omdathetkan/testrack/Boards/Backplane/Documentation/rework-reva-address-pullup.png

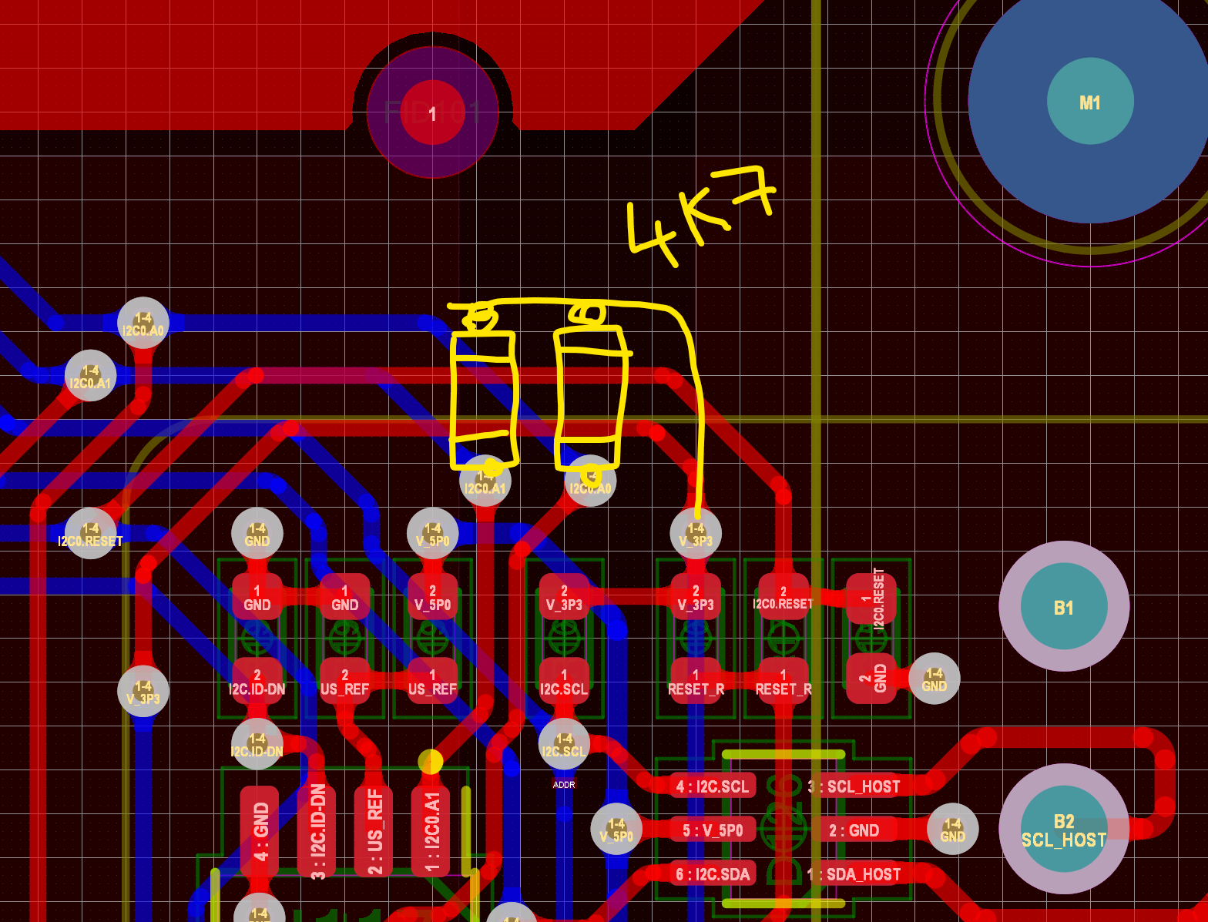
Boards/Backplane/Documentation/rework-reva-address-pullup.png
