omdathetkan/testrack/Boards/Backplane/Documentation/rework-reva-i2cmux.png

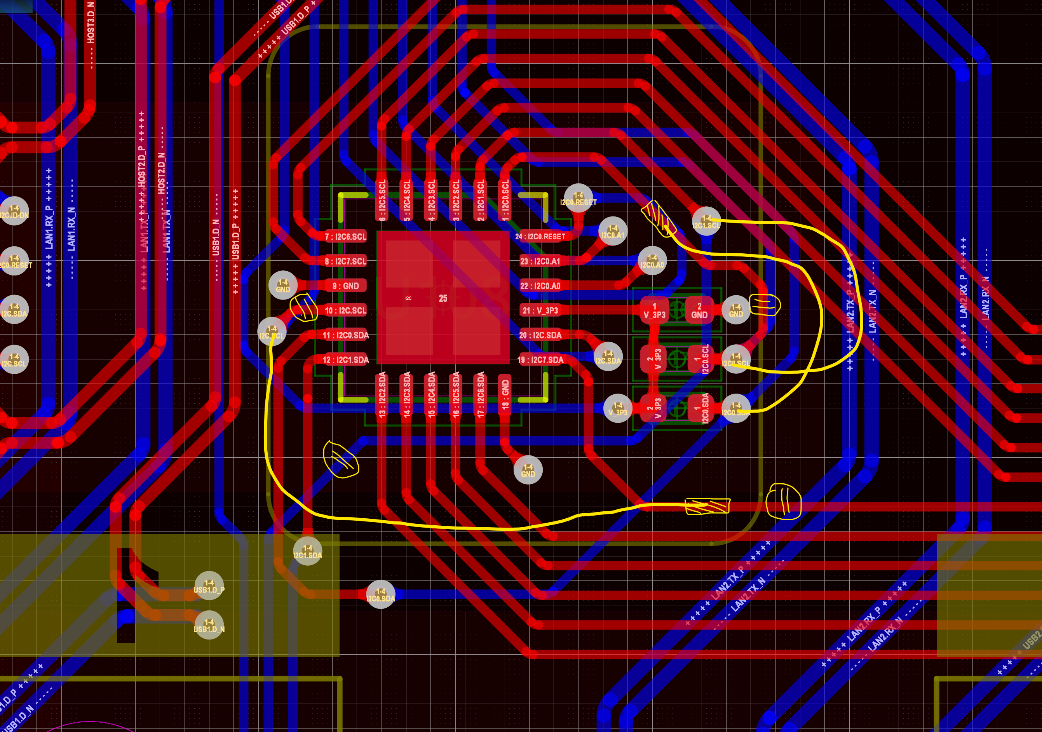
Boards/Backplane/Documentation/rework-reva-i2cmux.png
