omdathetkan/testrack/Boards/Host - CM4/Frontpanel/render.png

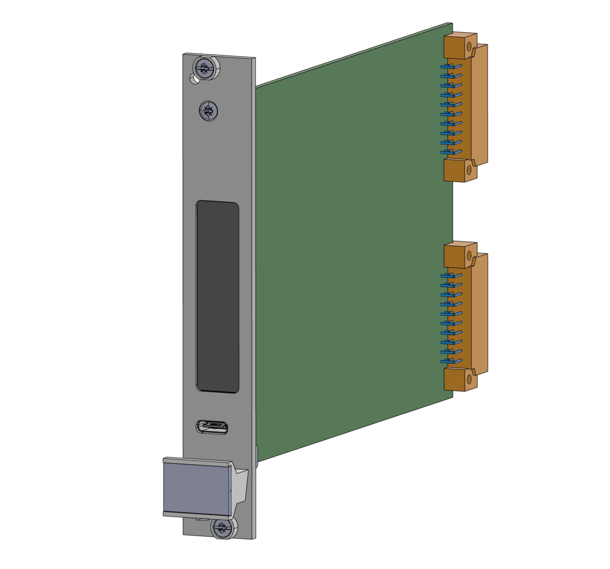
Boards/Host - CM4/Frontpanel/render.png
