omdathetkan/testrack/Boards/Module - Breakout/Documentation/mounting-3.jpeg

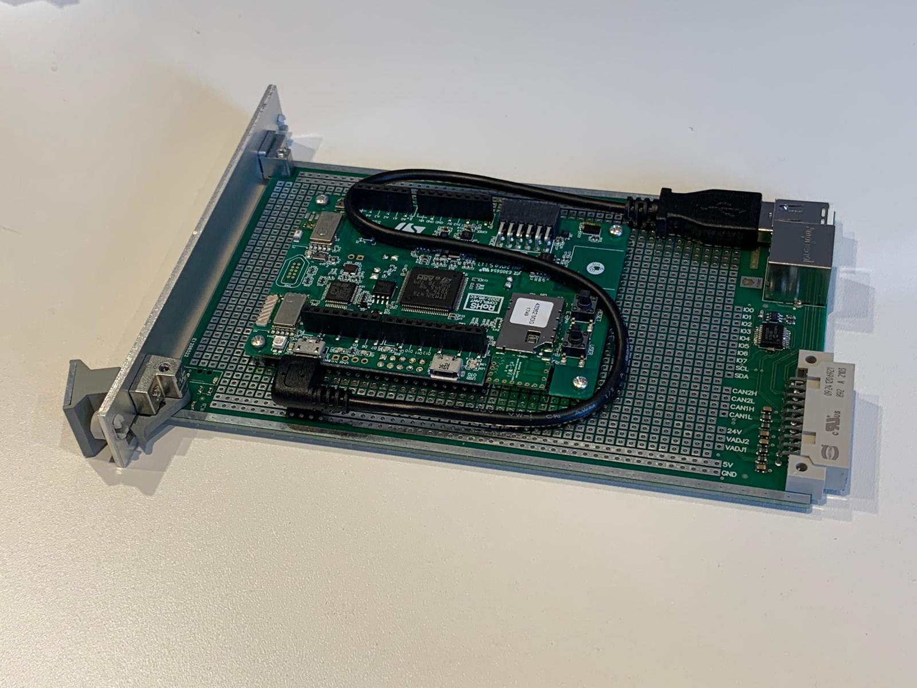
Boards/Module - Breakout/Documentation/mounting-3.jpeg
