omdathetkan/testrack/Mechanical/Shielded Module 2s/image (29).png

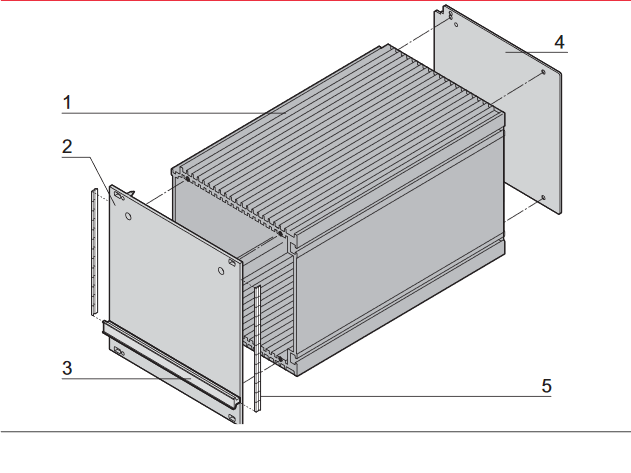
Mechanical/Shielded Module 2s/image (29).png
