omdathetkan/testrack/Mechanical/Shielded Module 2s/image (30).png

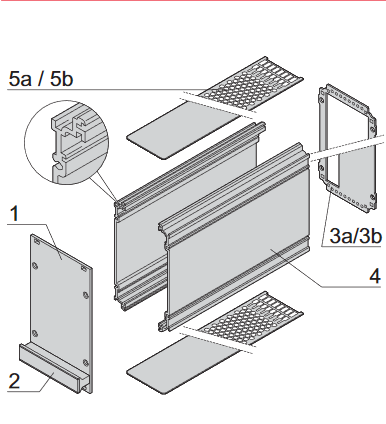
Mechanical/Shielded Module 2s/image (30).png
