omdathetkan/testrack/Mechanical/Shielded Module 2s/image (31).png

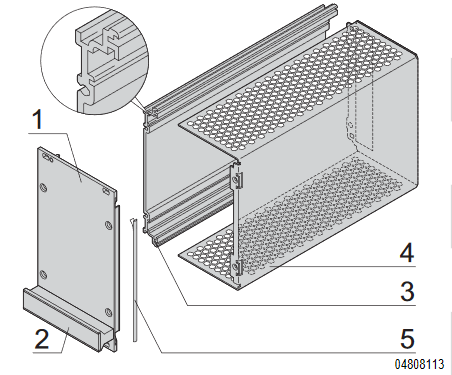
Mechanical/Shielded Module 2s/image (31).png
