omdathetkan/testrack/Boards/Module - Breakout/Rev A.3/FAB H-00491-00-A.3/Validation/Electrical Rules Check.html

Altium

# Electrical Rule Check Report

Date: | | 24-3-2021
Time: | | 10:04:07
Filename: | | C:\Users\Joris\AppData\Local\TempReleases\Snapshot\2\Fabrication\Validation\Electrical Rules Check.html

Class | Document | Message
Error | H-00491 - Top.SchDoc | LAN_TX_N contains Output Pin and Bidirectional Sheet Entry objects (Pin J11-2, Sheet Entry CONNECTOR-LAN_TX_N(I/O)).
Error | H-00491 - Top.SchDoc | LAN_TX_P contains Output Pin and Bidirectional Sheet Entry objects (Pin J11-1, Sheet Entry CONNECTOR-LAN_TX_P(I/O)).
Error | SCH-00005-6.SchDoc | Net CANA_N has only one pin (Pin P1-A7)
Error | SCH-00005-6.SchDoc | Net CANA_P has only one pin (Pin P1-B7)
Error | SCH-00005-6.SchDoc | Net CANB_N has only one pin (Pin P1-A8)
Error | SCH-00005-6.SchDoc | Net CANB_P has only one pin (Pin P1-B8)
Error | H-00491 - Top.SchDoc | Net GPIO0 has only one pin (Pin U10-12)
Error | H-00491 - Top.SchDoc | Net GPIO1 has only one pin (Pin U10-13)
Error | H-00491 - Top.SchDoc | Net GPIO2 has only one pin (Pin U10-14)
Error | H-00491 - Top.SchDoc | Net GPIO3 has only one pin (Pin U10-15)
Error | H-00491 - Top.SchDoc | Net GPIO4 has only one pin (Pin U10-16)
Error | H-00491 - Top.SchDoc | Net GPIO5 has only one pin (Pin U10-17)
Error | H-00491 - Top.SchDoc | Net GPIO6 has only one pin (Pin U10-18)
Error | H-00491 - Top.SchDoc | V_5P0 contains Output Pin and Output Sheet Entry objects (Pin U10-3, Sheet Entry CONNECTOR-V_5P0(Output)).
Error | H-00491 - Top.SchDoc | V_5P0 contains Output Pin and Power Pin objects (Pin U10-3, Pin U10-20, Pin U11-6).
Error | H-00491 - Top.SchDoc | V_5P0 contains Power Pin and Output Sheet Entry objects (Pin U10-20, Pin U11-6, Sheet Entry CONNECTOR-V_5P0(Output)).
Warning | H-00491 - Top.SchDoc | Net I2C_SCL has no driving source (Pin P1-B4, Pin R10-2, Pin U10-1, Pin U11-1)
Warning | H-00491 - Top.SchDoc | Net LAN_RX_N has no driving source (Pin J11-6, Pin P1-A1)
Warning | H-00491 - Top.SchDoc | Net LAN_RX_P has no driving source (Pin J11-3, Pin P1-B1)

Back to top
