omdathetkan/testrack/Boards/Module - Breakout/Rev A.3/FAB H-00491-00-A.3/Validation/Environment configuration compliance check.html

Altium

# Environment compilance report for Project H-00491.PrjPcb

Date: | | 24-3-2021
Time: | | 10:04:06

## Schematic documents

File | Status | Details
C:\Users\Joris\AppData\Local\TempReleases\Snapshot\2\Schematics\H-00491 - Top.SchDoc | Check passed | Item uses correct schematic template
C:\Users\Joris\AppData\Local\TempReleases\Snapshot\2\Managed\Sheets\A4F2CE20-EC05-4DC9-9731-BAFB31F29386\SCH-00005-6.SchDoc | Check passed | Item uses correct schematic template

Back to top

## Parts

Document | Part | Status | Description
H-00491 - Top.SchDoc | C0603C104K5RACTU(C10) | Check passed | Part comes from a server
H-00491 - Top.SchDoc | C0603C104K5RACTU(C11) | Check passed | Part comes from a server
H-00491 - Top.SchDoc | SML-E12M8W(D10) | Check passed | Part comes from a server
H-00491 - Top.SchDoc | SML-E12M8W(D11) | Check passed | Part comes from a server
H-00491 - Top.SchDoc | FIDUCIAL(FID10) | Check passed | Part comes from a server
H-00491 - Top.SchDoc | FIDUCIAL(FID11) | Check passed | Part comes from a server
H-00491 - Top.SchDoc | FIDUCIAL(FID12) | Check passed | Part comes from a server
H-00491 - Top.SchDoc | LOGO-HIBER(G10) | Check passed | Part comes from a server
H-00491 - Top.SchDoc | HIBER-PARTNUMBER(G11) | Check passed | Part comes from a server
H-00491 - Top.SchDoc | 67643-3910(J10) | Check passed | Part comes from a server
H-00491 - Top.SchDoc | RJHSE5E80(J11) | Check passed | Part comes from a server
H-00491 - Top.SchDoc | 20817-443(MP10) | Check passed | Part comes from a server
H-00491 - Top.SchDoc | 5151094F(MP11) | Check passed | Part comes from a server
H-00491 - Top.SchDoc | TITLE-BLOCK(PCB10) | Check passed | Part comes from a server
H-00491 - Top.SchDoc | CRCW06034K70FKEA(R10) | Check passed | Part comes from a server
H-00491 - Top.SchDoc | CRCW06034K70FKEA(R11) | Check passed | Part comes from a server
H-00491 - Top.SchDoc | CRCW06034K70FKEA(R12) | Check passed | Part comes from a server
H-00491 - Top.SchDoc | CRCW06034K70FKEA(R13) | Check passed | Part comes from a server
H-00491 - Top.SchDoc | MCP23008-E/SS(U10) | Check passed | Part comes from a server
H-00491 - Top.SchDoc | 24AA025E64T-I/OT(U11) | Check passed | Part comes from a server
SCH-00005-6.SchDoc | C0805C474K5RACTU(C1) | Check passed | Part comes from a server
SCH-00005-6.SchDoc | C0805C474K5RACTU(C2) | Check passed | Part comes from a server
SCH-00005-6.SchDoc | C0603W102KDRACAUTO(C3) | Check passed | Part comes from a server
SCH-00005-6.SchDoc | C0805C474K5RACTU(C4) | Check passed | Part comes from a server
SCH-00005-6.SchDoc | C0805C474K5RACTU(C5) | Check passed | Part comes from a server
SCH-00005-6.SchDoc | BLM21SP700SH1D(L1) | Check passed | Part comes from a server
SCH-00005-6.SchDoc | BLM21SP700SH1D(L2) | Check passed | Part comes from a server
SCH-00005-6.SchDoc | BLM21SP700SH1D(L3) | Check passed | Part comes from a server
SCH-00005-6.SchDoc | BLM21SP700SH1D(L4) | Check passed | Part comes from a server
SCH-00005-6.SchDoc | EUROCARD_160X100(MH1) | Check passed | Part comes from a server
SCH-00005-6.SchDoc | NET-TIE(NT1) | Check passed | Part comes from a server
SCH-00005-6.SchDoc | 09241206921(P1) | Check passed | Part comes from a server
SCH-00005-6.SchDoc | TNPW060310K0BEEA(R1) | Check passed | Part comes from a server

Back to top
